silvagustin/taller_de_proyecto_1/docs/images/Imagenes ilustrativas/foto.jpg

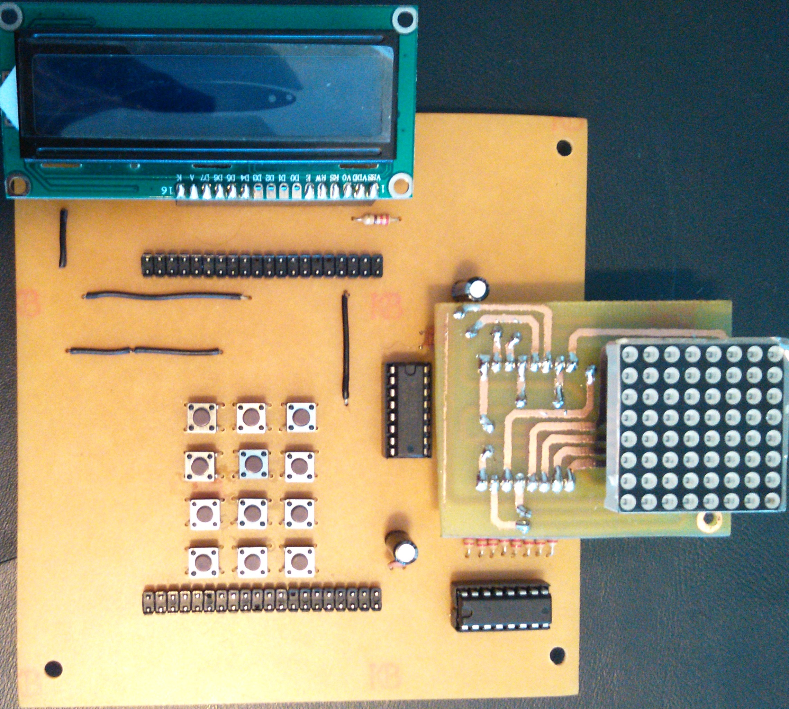
docs/images/Imagenes ilustrativas/foto.jpg
