silvagustin/taller_de_proyecto_1/docs/images/Esquematicos/Esquematico SubPoncho.png

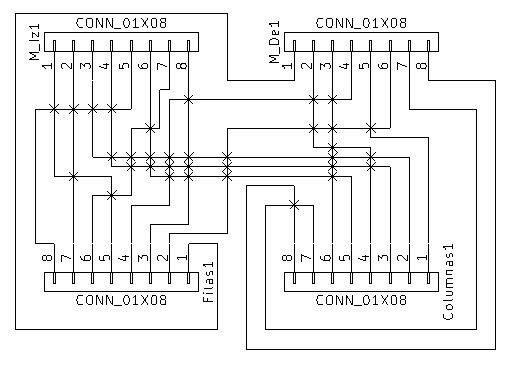
docs/images/Esquematicos/Esquematico SubPoncho.png
