silvagustin/taller_de_proyecto_1/docs/images/Imagenes ilustrativas/figura 1.png

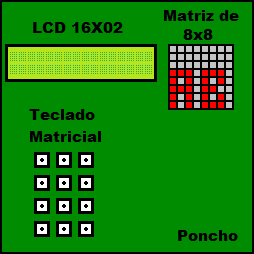
docs/images/Imagenes ilustrativas/figura 1.png
