silvagustin/taller_de_proyecto_1/docs/images/Imagenes ilustrativas/figura x-x.png

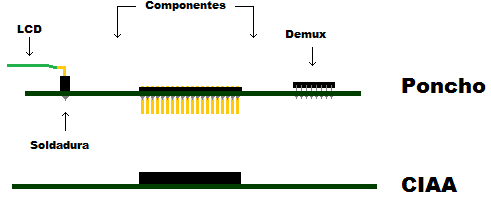
docs/images/Imagenes ilustrativas/figura x-x.png
