silvagustin/taller_de_proyecto_1/docs/images/Maquinas de Estado/MaquinaEstado - Funcion Enviar Texto.png

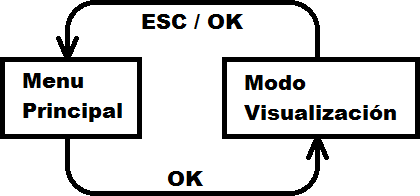
docs/images/Maquinas de Estado/MaquinaEstado - Funcion Enviar Texto.png
