silvagustin/taller_de_proyecto_1/docs/images/PCB/PCB_sobre-poncho.png

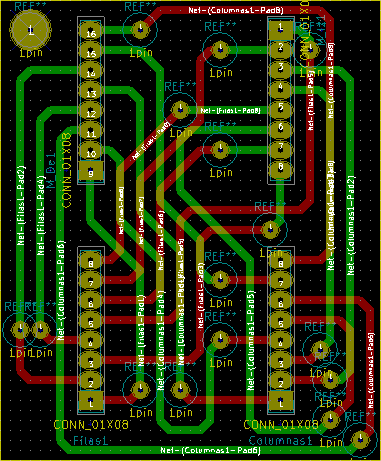
docs/images/PCB/PCB_sobre-poncho.png
