silvagustin/taller_de_proyecto_1/docs/images/PCB/PonchoInferior.png

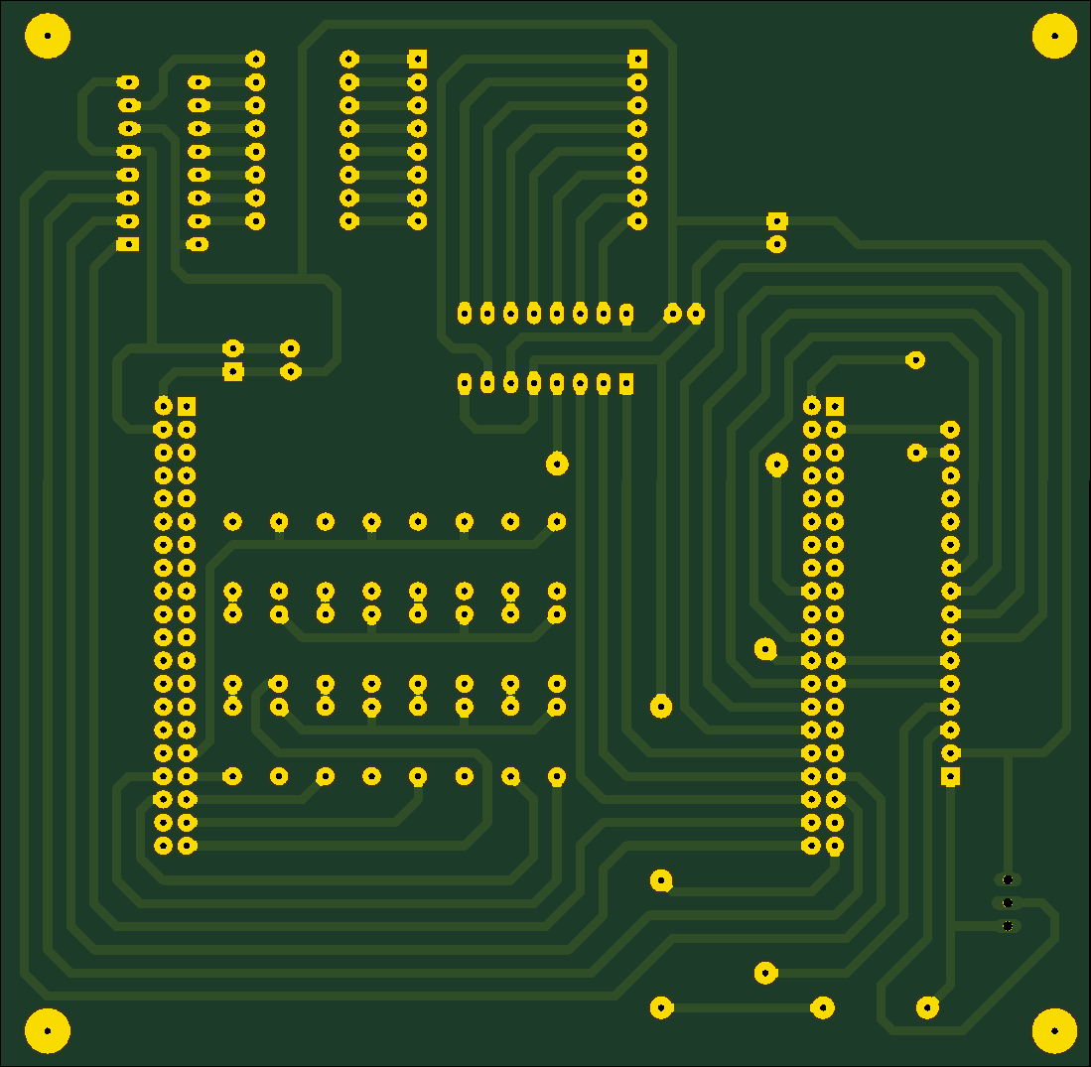
docs/images/PCB/PonchoInferior.png
