silvagustin/taller_de_proyecto_1/docs/images/PCB/PonchoSuperior.png

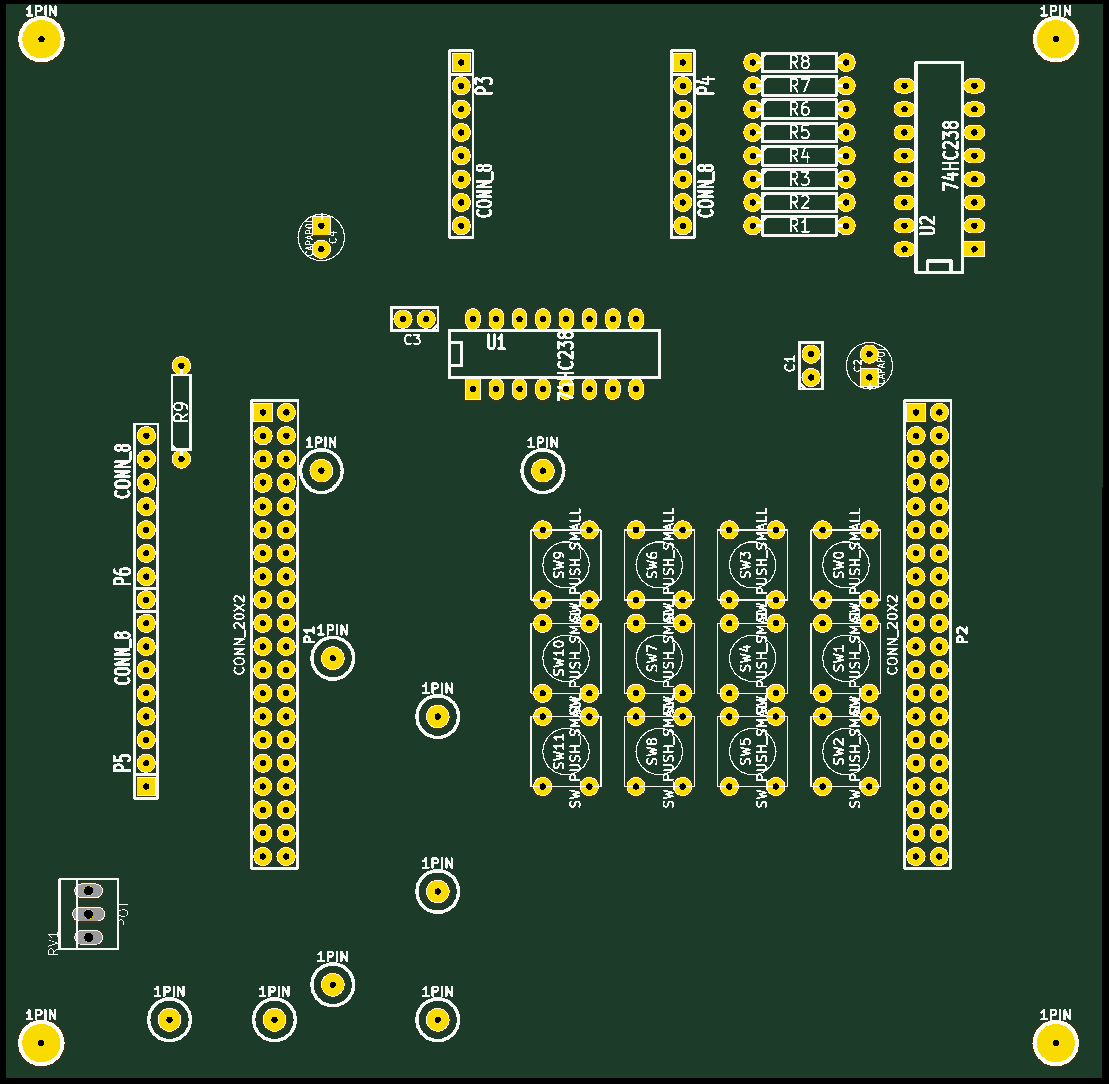
docs/images/PCB/PonchoSuperior.png
