silvagustin/taller_de_proyecto_1/docs/images/PCB/SubPoncho Inferior.png

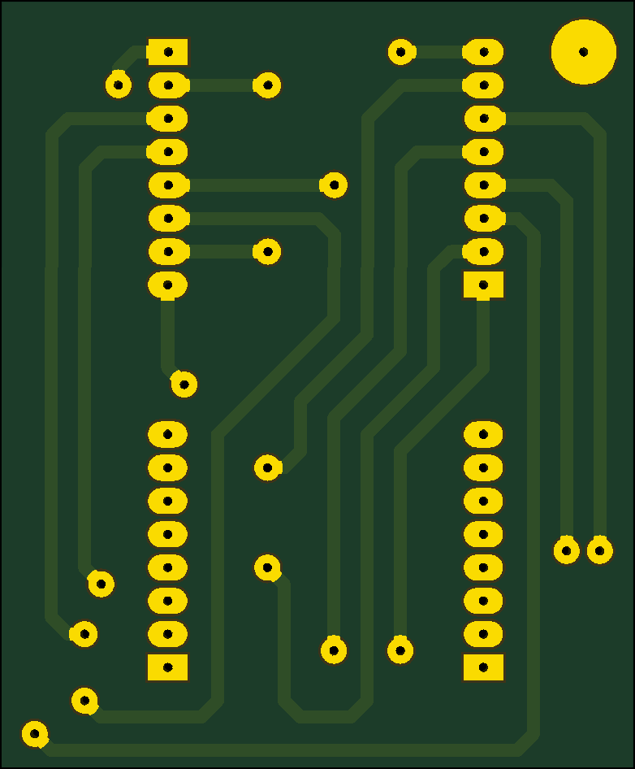
docs/images/PCB/SubPoncho Inferior.png
