silvagustin/taller_de_proyecto_1/firmware/FirmwareMatrizTecladoLCD/proyectos/poncho/inc/letrasMatriz.h

#define dimLetraY 6
#define dimLetraX 6

/*--------------------- Constantes de Matriz --------------------------*/
//LetrasMayus
const uint8_t letraA[dimLetraY][dimLetraX] = {
		{0,0,1,0,0,0},
		{0,1,0,1,0,0},
		{1,0,0,0,1,0},
		{1,1,1,1,1,0},
		{1,0,0,0,1,0},
		{1,0,0,0,1,0},
};
const uint8_t letraB[dimLetraY][dimLetraX] = {
		{1,1,1,0,0,0},
		{1,0,0,1,0,0},
		{1,1,1,1,0,0},
		{1,0,0,0,1,0},
		{1,0,0,0,1,0},
		{1,1,1,1,0,0},
};
const uint8_t letraC[dimLetraY][dimLetraX] = {
		{0,1,1,1,1,0},
		{1,0,0,0,0,0},
		{1,0,0,0,0,0},
		{1,0,0,0,0,0},
		{1,0,0,0,0,0},
		{0,1,1,1,1,0},
};
const uint8_t letraD[dimLetraY][dimLetraX] = {
		{1,1,1,0,0,0},
		{1,0,0,1,0,0},
		{1,0,0,0,1,0},
		{1,0,0,0,1,0},
		{1,0,0,1,0,0},
		{1,1,1,0,0,0},
};
const uint8_t letraE[dimLetraY][dimLetraX] = {
		{1,1,1,1,1,0},
		{1,0,0,0,0,0},
		{1,1,1,0,0,0},
		{1,0,0,0,0,0},
		{1,0,0,0,0,0},
		{1,1,1,1,1,0},
};
const uint8_t letraF[dimLetraY][dimLetraX] = {
		{1,1,1,1,1,0},
		{1,0,0,0,0,0},
		{1,1,1,0,0,0},
		{1,0,0,0,0,0},
		{1,0,0,0,0,0},
		{1,0,0,0,0,0},
};
const uint8_t letraG[dimLetraY][dimLetraX] = {
		{0,1,1,1,1,0},
		{1,0,0,0,0,0},
		{1,0,1,1,0,0},
		{1,0,0,0,1,0},
		{1,0,0,0,1,0},
		{1,1,1,1,1,0},
};
const uint8_t letraH[dimLetraY][dimLetraX] = {
		{1,0,0,0,1,0},
		{1,0,0,0,1,0},
		{1,1,1,1,1,0},
		{1,0,0,0,1,0},
		{1,0,0,0,1,0},
		{1,0,0,0,1,0},
};
const uint8_t letraI[dimLetraY][dimLetraX] = {
		{0,1,1,1,0,0},
		{0,0,1,0,0,0},
		{0,0,1,0,0,0},
		{0,0,1,0,0,0},
		{0,0,1,0,0,0},
		{0,1,1,1,0,0},
};
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
		{0,0,1,0,0,0},
		{0,0,1,0,0,0},
		{0,0,1,0,0,0},
		{0,0,1,0,0,0},
		{1,1,1,0,0,0},
};
const uint8_t espacio[dimLetraY][dimLetraX] = {
		{0,0,0,0,0,0},
		{0,0,0,0,0,0},
		{0,0,0,0,0,0},
		{0,0,0,0,0,0},
		{0,0,0,0,0,0},
		{0,0,0,0,0,0},
};
const uint8_t hashtag[dimLetraY][dimLetraX] = {
		{0,0,0,0,0,0},
		{0,1,0,1,0,0},
		{1,1,1,1,1,0},
		{0,1,0,1,0,0},
		{1,1,1,1,1,0},
		{0,1,0,1,0,0},
};
const uint8_t dosPuntos[dimLetraY][dimLetraX] = {
		{0,0,0,0,0,0},
		{0,0,0,0,0,0},
		{0,0,1,0,0,0},
		{0,0,0,0,0,0},
		{0,0,0,0,0,0},
		{0,0,1,0,0,0},
};
const uint8_t puntoYcoma[dimLetraY][dimLetraX] = {
		{0,0,0,0,0,0},
		{0,0,0,0,0,0},
		{0,0,1,0,0,0},
		{0,0,0,0,0,0},
		{0,0,1,0,0,0},
		{0,1,0,0,0,0},
};
const uint8_t menor[dimLetraY][dimLetraX] = {
		{0,0,0,0,0,0},
		{0,0,1,0,0,0},
		{0,1,0,0,0,0},
		{1,0,0,0,0,0},
		{0,1,0,0,0,0},
		{0,0,1,0,0,0},
};
const uint8_t mayor[dimLetraY][dimLetraX] = {
		{0,0,0,0,0,0},
		{0,0,1,0,0,0},
		{0,0,0,1,0,0},
		{0,0,0,0,1,0},
		{0,0,0,1,0,0},
		{0,0,1,0,0,0},
};
const uint8_t guionBajo[dimLetraY][dimLetraX] = {
		{0,0,0,0,0,0},
		{0,0,0,0,0,0},
		{0,0,0,0,0,0},
		{0,0,0,0,0,0},
		{0,0,0,0,0,0},
		{1,1,1,1,1,0},
};
/*-------------------------------------------*/
