silvagustin/taller_de_proyecto_1/firmware/FirmwareMatrizTecladoLCD/examples/blinking_echo/src/blinking_echo.c

/* Copyright 2014, Mariano Cerdeiro
 * Copyright 2014, Pablo Ridolfi
 * Copyright 2014, Juan Cecconi
 * Copyright 2014, Gustavo Muro
 *
 * This file is part of CIAA Firmware.
 *
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
 * 3. Neither the name of the copyright holder nor the names of its
 *    contributors may be used to endorse or promote products derived from this
 *    software without specific prior written permission.
 *
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
 */

/** \brief Blinking_echo example source file
 **
 ** This is a mini example of the CIAA Firmware to test the periodical
 ** task excecution and serial port funcionality.
 ** To run this sample in x86 plataform you must enable the funcionality of
 ** uart device setting a value of une or more of folowing macros defined
 ** in header file modules/plataforms/x86/inc/ciaaDriverUart_Internal.h
 **/

/** \addtogroup CIAA_Firmware CIAA Firmware
 ** @{ */
/** \addtogroup Examples CIAA Firmware Examples
 ** @{ */
/** \addtogroup Blinking Blinking_echo example source file
 ** @{ */

/*
 * Initials     Name
 * ---------------------------
 * MaCe         Mariano Cerdeiro
 * PR           Pablo Ridolfi
 * JuCe         Juan Cecconi
 * GMuro        Gustavo Muro
 */

/*
 * modification history (new versions first)
 * -----------------------------------------------------------
 * 20141019 v0.0.2   JuCe add printf in each task,
 *                        remove trailing spaces
 * 20140731 v0.0.1   PR   first functional version
 */

/*==================[inclusions]=============================================*/
#include "os.h"               /* <= operating system header */
#include "ciaaPOSIX_stdio.h"  /* <= device handler header */
#include "ciaaPOSIX_string.h" /* <= string header */
#include "ciaak.h"            /* <= ciaa kernel header */
#include "blinking_echo.h"         /* <= own header */

/*==================[macros and definitions]=================================*/

/*==================[internal data declaration]==============================*/

/*==================[internal functions declaration]=========================*/

/*==================[internal data definition]===============================*/
/** \brief File descriptor for digital input ports
 *
 * Device path /dev/dio/in/0
 */
static int32_t fd_in;

/** \brief File descriptor for digital output ports
 *
 * Device path /dev/dio/out/0
 */
static int32_t fd_out;

/** \brief File descriptor of the USB uart
 *
 * Device path /dev/serial/uart/1
 */
static int32_t fd_uart1;

/** \brief File descriptor of the RS232 uart
 *
 * Device path /dev/serial/uart/2
 */
static int32_t fd_uart2;

/** \brief Periodic Task Counter
 *
 */
static uint32_t Periodic_Task_Counter;

/*==================[external data definition]===============================*/

/*==================[internal functions definition]==========================*/

/*==================[external functions definition]==========================*/
/** \brief Main function
 *
 * This is the main entry point of the software.
 *
 * \returns 0
 *
 * \remarks This function never returns. Return value is only to avoid compiler
 *          warnings or errors.
 */
int main(void)
{
   /* Starts the operating system in the Application Mode 1 */
   /* This example has only one Application Mode */
   StartOS(AppMode1);

   /* StartOs shall never returns, but to avoid compiler warnings or errors
    * 0 is returned */
   return 0;
}

/** \brief Error Hook function
 *
 * This fucntion is called from the os if an os interface (API) returns an
 * error. Is for debugging proposes. If called this function triggers a
 * ShutdownOs which ends in a while(1).
 *
 * The values:
 *    OSErrorGetServiceId
 *    OSErrorGetParam1
 *    OSErrorGetParam2
 *    OSErrorGetParam3
 *    OSErrorGetRet
 *
 * will provide you the interface, the input parameters and the returned value.
 * For more details see the OSEK specification:
 * http://portal.osek-vdx.org/files/pdf/specs/os223.pdf
 *
 */
void ErrorHook(void)
{
   ciaaPOSIX_printf("ErrorHook was called\n");
   ciaaPOSIX_printf("Service: %d, P1: %d, P2: %d, P3: %d, RET: %d\n", OSErrorGetServiceId(), OSErrorGetParam1(), OSErrorGetParam2(), OSErrorGetParam3(), OSErrorGetRet());
   ShutdownOS(0);
}

/** \brief Initial task
 *
 * This task is started automatically in the application mode 1.
 */
TASK(InitTask)
{
   /* init CIAA kernel and devices */
   ciaak_start();

   ciaaPOSIX_printf("Init Task...\n");
   /* open CIAA digital inputs */
   fd_in = ciaaPOSIX_open("/dev/dio/in/0", ciaaPOSIX_O_RDONLY);

   /* open CIAA digital outputs */
   fd_out = ciaaPOSIX_open("/dev/dio/out/0", ciaaPOSIX_O_RDWR);

   /* open UART connected to USB bridge (FT2232) */
   fd_uart1 = ciaaPOSIX_open("/dev/serial/uart/1", ciaaPOSIX_O_RDWR);

   /* open UART connected to RS232 connector */
   fd_uart2 = ciaaPOSIX_open("/dev/serial/uart/2", ciaaPOSIX_O_RDWR);

   /* change baud rate for uart usb */
   ciaaPOSIX_ioctl(fd_uart1, ciaaPOSIX_IOCTL_SET_BAUDRATE, (void *)ciaaBAUDRATE_115200);

   /* change FIFO TRIGGER LEVEL for uart usb */
   ciaaPOSIX_ioctl(fd_uart1, ciaaPOSIX_IOCTL_SET_FIFO_TRIGGER_LEVEL, (void *)ciaaFIFO_TRIGGER_LEVEL3);

   /* activate example tasks */
   Periodic_Task_Counter = 0;
   SetRelAlarm(ActivatePeriodicTask, 200, 200);

   /* Activates the SerialEchoTask task */
   ActivateTask(SerialEchoTask);

   /* end InitTask */
   TerminateTask();
}

/** \brief Serial Echo Task
 *
 * This tasks waits for input data from fd_uart1 and writes the received data
 * to fd_uart1 and fd_uart2. This taks alos blinkgs the output 5.
 *
 */
TASK(SerialEchoTask)
{
   int8_t buf[20];   /* buffer for uart operation              */
   uint8_t outputs;  /* to store outputs status                */
   int32_t ret;      /* return value variable for posix calls  */

   ciaaPOSIX_printf("SerialEchoTask...\n");
   /* send a message to the world :) */
   char message[] = "Hi! :)\nSerialEchoTask: Waiting for characters...\n";
   ciaaPOSIX_write(fd_uart1, message, ciaaPOSIX_strlen(message));

   while(1)
   {
      /* wait for any character ... */
      ret = ciaaPOSIX_read(fd_uart1, buf, 20);

      if(ret > 0)
      {
         /* ... and write them to the same device */
         ciaaPOSIX_write(fd_uart1, buf, ret);

         /* also write them to the other device */
         ciaaPOSIX_write(fd_uart2, buf, ret);
      }

      /* blink output 5 with each loop */
      ciaaPOSIX_read(fd_out, &outputs, 1);
      outputs ^= 0x20;
      ciaaPOSIX_write(fd_out, &outputs, 1);
   }
}

/** \brief Periodic Task
 *
 * This task is activated by the Alarm ActivatePeriodicTask.
 * This task copies the status of the inputs bits 0..3 to the output bits 0..3.
 * This task also blinks the output 4
 */
TASK(PeriodicTask)
{
   /*
    * Example:
    *    Read inputs 0..3, update outputs 0..3.
    *    Blink output 4
    */

   /* variables to store input/output status */
   uint8_t inputs = 0, outputs = 0;

   /* read inputs */
   ciaaPOSIX_read(fd_in, &inputs, 1);

   /* read outputs */
   ciaaPOSIX_read(fd_out, &outputs, 1);

   /* update outputs with inputs */
   outputs &= 0xF0;
   outputs |= inputs & 0x0F;

   /* blink */
   outputs ^= 0x10;

   /* write */
   ciaaPOSIX_write(fd_out, &outputs, 1);

   /* Print Task info */
   Periodic_Task_Counter++;
   ciaaPOSIX_printf("Periodic Task: %d\n", Periodic_Task_Counter);

   /* end PeriodicTask */
   TerminateTask();
}

/** @} doxygen end group definition */
/** @} doxygen end group definition */
/** @} doxygen end group definition */
/*==================[end of file]============================================*/
